krotik/spieljunge/pics/spieljunge_002.jpg

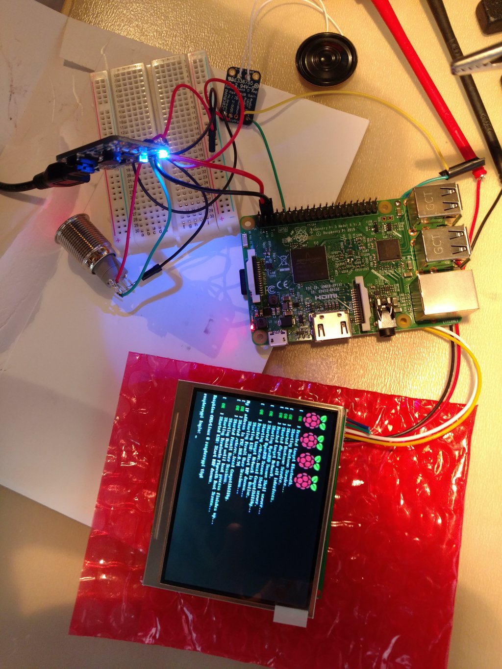
pics/spieljunge_002.jpg
