krotik/spieljunge/pics/spieljunge_021.jpg

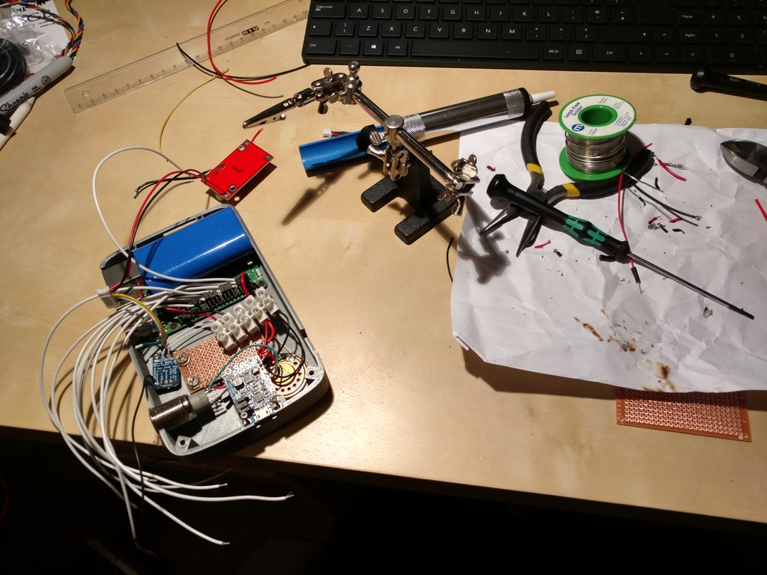
pics/spieljunge_021.jpg
