krotik/spieljunge/pics/spieljunge_022.jpg

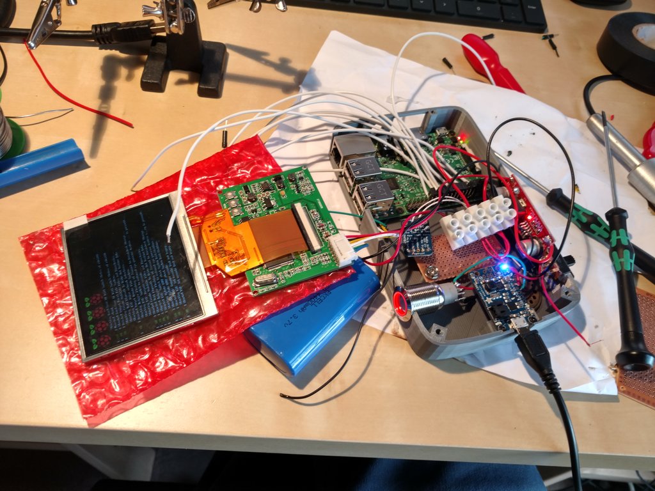
pics/spieljunge_022.jpg
