krotik/spieljunge/pics/spieljunge_025.jpg

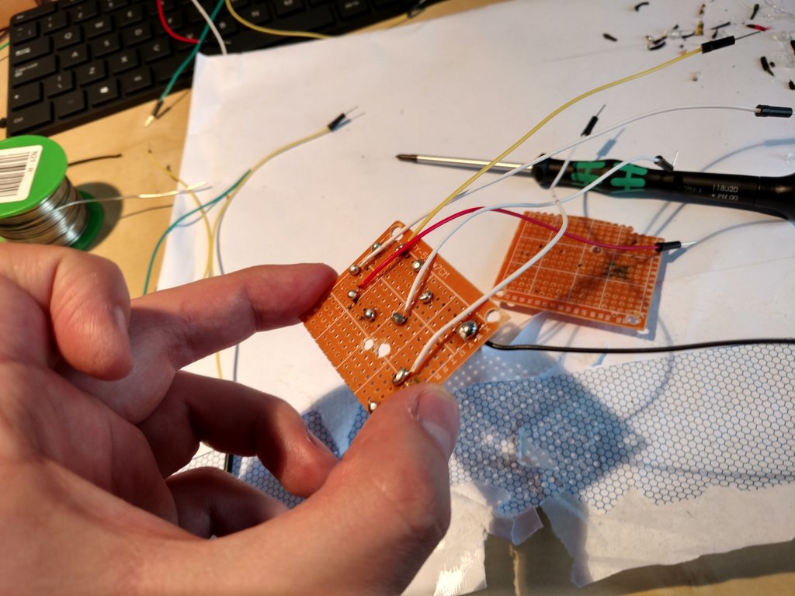
pics/spieljunge_025.jpg
