krotik/spieljunge/pics/spieljunge_029.jpg

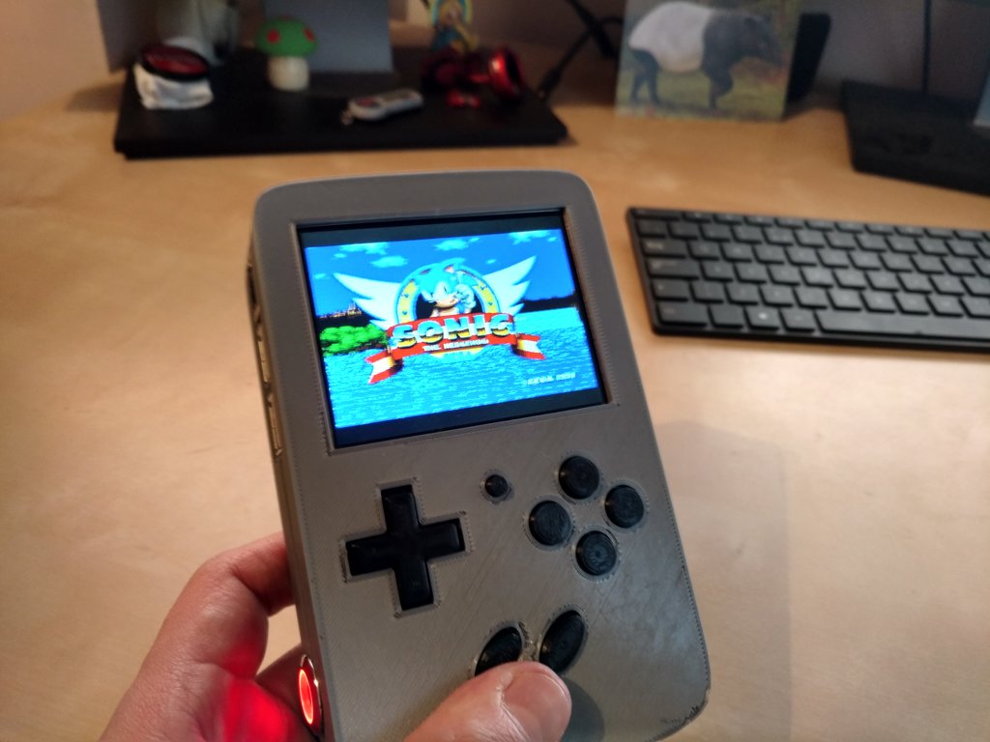
pics/spieljunge_029.jpg
